Akshat412/SDP-Team-31/Data/Fall 2022/app_test.xlsx

Distance | Strength | Success | Distance | Strength | Success
1 | -70 | 1 | 3 | -83 | 1
2 | -76 | 1
3 | -87 | 1
