Akshat412/SDP-Team-31/Data/Spring 2023/Soft/collision_test_soft_2nd_4_21.csv

Magnitude
0.64
1.01
1.4
1.72
1.41
1.46
12
1.98
1.89
2.04
2.02
2.18
1.58
1.99
1.77
2.04
1.97
1.67
1.96
1.96
1.98
2.06
1.74
1.96
1.84
1.99
1.69
1.83
1.9
1.83
1.96
1.7
1.93
1.77
2.02
1.81
1.89
2.06
1.39
1.55
1.87
1.61
1.49
1.67
1.89
1.62
1.68
1.34
1.72
1.76
1.86
1.9
1.69
1.46
1.67
1.43
1.8
1.62
1.85
1.39
1.69
1.58
1.79
1.57
1.66
1.69
1.39
1.21
1.5
1.68
1.57
1.38
1.5
1.38
1.5
1.41
1.42
1.42
1.71
1.39
1.57
1.8
1.86
1.43
1.62
1.4
1.6
1.22
1
1.39
1.62
1.48
1.49
1.18
1.24
1.6
1.31
1.27
1.69
1.3
1.2
1.38
1.06
1.12
1.27
1.43
1.43
1.5
1.18
1.43
1.19
1.33
1.43
1.08
1.52
1.27
1.2
1.15
1.28
1.33
1.16
1.18
1.4
1.23
0.98
1.15
1.43
1
0.88
0.71
0.78
1.4
1.32
1.06
1.2
1.1
1.02
1.33
1.42
1.26
1.06
0.75
0.88
1.18
1.03
1.19
1.02
1.23
1.21
1.06
0.78
0.84
0.98
1.18
1.13
1
0.97
0.79
1.18
0.93
0.83
0.79
0.83
1.08
0.98
1.16
0.75
0.98
0.93
1.13
1
0.84
0.93
0.62
1.21
1.06
0.88
0.75
0.98
0.88
1.18
0.77
1.03
1.02
0.9
1
0.44
1.1
1.2
1.1
0.81
0.75
0.84
0.92
0.72
0.6
1.36
0.98
0.81
0.89
0.97
1.1
1.04
1.1
0.84
0.93
0.92
0.84
0.84
1.1
0.71
1.15
1.08
0.97
0.88
1.09
1.08
1.21
0.93
1.49
1.14
1.22
1.17
0.44
0.9
1.1
0.89
0.71
1.35
0.89
1.08
1.15
1.1
0.89
1.22
1.07
0.89
1.1
1.21
0.77
0.95
0.84
0.93
1.5
1.03
1.21
1.24
1.07
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
