Akshat412/SDP-Team-31/Data/Spring 2023/Soft/collision_test_soft_4_21.csv

Magnitude
0.03
1.06
1.42
1.48
1.4
1.38
1.04
1.41
1.52
1.34
1.38
1.38
1.43
1.1
1.29
1.31
1.47
1.37
1.81
1.4
1.57
1.76
1.29
1.48
1.48
1.67
1.62
1.5
1.49
1.67
1.18
1.69
1.65
1.67
1.21
1.48
1.57
1.5
1.48
1.47
1.57
1.47
1.68
1.47
1.29
1.77
1.18
1.86
1.77
1.4
1.57
1.37
1.47
1.57
1.57
1.57
1.58
1.57
1.47
1.38
1.7
1.67
1.47
1.47
1.51
1.28
1.57
1.19
1.57
1.58
1.19
1.31
1.28
1.67
1.6
1.47
1.49
1.67
1.52
1.68
1.58
1.52
1.27
1.69
1.47
1.59
1.18
1.55
1.5
1.69
1.42
1.27
1.29
1.47
1.31
1.26
1.76
1.67
1.51
1.47
1.27
1.6
1.08
1.67
1.37
1.48
1.47
1.39
1.39
1.47
1.6
1.27
1.47
1.48
1.48
1.47
1.47
1.6
1.58
1.38
1.29
1.31
1.33
1.02
1.67
1.52
1.48
1.67
1
1.47
1.47
1.69
1.47
1.18
1.58
1.38
1.67
1.41
1.77
1.48
1.4
1.81
1.37
1.31
1.68
1.37
1.57
1.38
1.39
1.83
1.28
1.28
1.36
1.28
1.29
1.57
1.41
1.21
1.47
1.42
1.37
1.5
1.39
1.29
1.4
1.47
1.28
1.15
1.57
1.37
1.69
1.38
1.38
1.39
1.2
1.39
1.08
1.27
1.38
1.41
1.37
1.2
1.27
1.27
1.27
1.48
1.1
1.33
1.3
1.19
0.98
1.38
1.28
1.57
1.39
1.48
1.38
1.27
1.77
1.18
1.38
1.52
1.37
1.27
1.31
1.47
1.27
1.4
1.76
1.24
1.33
1.38
1.61
1.18
1.18
1.47
1.29
1.49
1.23
1.31
1.4
1.21
1.38
1.31
1.4
1.5
1.08
1.47
1.57
1.38
1.52
1.47
1.62
1.19
1.76
1.38
1.43
1.29
1.46
1.39
1.18
1.33
1.43
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
