Akshat412/SDP-Team-31/Data/Spring 2023/collision_test_4_21.csv

Magnitude | Sampled at 3200 Hz
1.35
1.35
1.62
1.57
1.29
1.55
1.58
1.46
1.31
1.54
1.08
1.44
1.52
1.52
1.11
1.41
1.76
1.26
1.29
1.65
1.16
1.61
1.41
1.46
1.34
1.28
1.2
1.55
1.16
1.41
1.14
1.21
1.12
1.16
1.42
1.27
1.51
1.51
1.25
0.98
1.42
1.37
1.28
1.42
0.39
1.13
1.09
1.08
1.19
1.25
1.18
1.32
1.43
1.58
1.4
1.12
1.16
1.27
1
1.29
1.46
1.26
1.07
1.35
1.1
1.37
1
1.37
1.47
1.31
1.21
1.33
0.93
1.15
1.15
1.29
1.59
1.18
1.36
1.34
0.98
1.1
1.52
1.26
1.18
1.2
1.48
1.64
1.78
1.15
1.26
1.69
0.89
1.18
1.46
1.48
1.74
1.27
1.46
1.37
1.27
1.14
1.43
1
1.56
1.34
1.29
1.67
1.29
1.46
1.15
1.24
1.22
1.28
1.51
1.42
1.2
1.25
1.39
1.12
1.27
1.31
1.51
1.22
1.32
1.48
1.5
1.38
1.29
1.22
1.22
1.21
1.25
1.21
1.52
1.38
1.18
1.44
1.43
1.55
1.42
1.39
1.56
1.38
1.4
1.42
1.35
1.29
1.47
1.31
1.62
1.13
1.31
1.51
1.4
1.19
1.32
1.51
1.06
1.46
1.41
1.4
1.42
1.26
1.27
1.34
1.27
1.29
1.61
1.27
1.51
1.42
1.1
1.18
1.18
1.62
1.46
1.2
1.26
1.62
1.53
1.29
1.69
1.43
1.32
1.46
1.16
0.92
1.36
1.18
1.18
1.25
1.43
1.31
1.18
1.22
1.34
1.33
1.2
1.23
1.53
1.24
1.48
1.41
1.72
1.15
0.98
1.43
1.32
1.18
1.46
1.66
1.63
1.51
1.52
1.86
1.99
0.93
1.29
1.29
1.48
1.61
1.24
1.18
1.31
1.39
1.58
1.27
1.61
1.63
1.51
1.26
1.27
1.39
1.64
1.23
1.18
1.63
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
