Akshat412/SDP-Team-31/Firmware/Testing/bleTest/bleTest.ino

#include <Arduino.h>
#include <SPI.h>
#include "Adafruit_BLE.h"
#include "Adafruit_BluefruitLE_SPI.h"
#include "Adafruit_BluefruitLE_UART.h"

#include "BluefruitConfig.h"

/*=========================================================================
    APPLICATION SETTINGS

? ? FACTORYRESET_ENABLE? ?  Perform a factory reset when running this sketch
? ?
? ?                         Enabling this will put your Bluefruit LE module
                            in a 'known good' state and clear any config
                            data set in previous sketches or projects, so
? ?                         running this at least once is a good idea.
? ?
? ?                         When deploying your project, however, you will
                            want to disable factory reset by setting this
                            value to 0.? If you are making changes to your
? ?                         Bluefruit LE device via AT commands, and those
                            changes aren't persisting across resets, this
                            is the reason why.? Factory reset will erase
                            the non-volatile memory where config data is
                            stored, setting it back to factory default
                            values.
? ? ? ?
? ?                         Some sketches that require you to bond to a
                            central device (HID mouse, keyboard, etc.)
                            won't work at all with this feature enabled
                            since the factory reset will clear all of the
                            bonding data stored on the chip, meaning the
                            central device won't be able to reconnect.
    -----------------------------------------------------------------------*/
    #define FACTORYRESET_ENABLE      1
/*=========================================================================*/


/* ...hardware SPI, using SCK/MOSI/MISO hardware SPI pins and then user selected CS/IRQ/RST */
Adafruit_BluefruitLE_SPI ble(BLUEFRUIT_SPI_CS, BLUEFRUIT_SPI_IRQ, BLUEFRUIT_SPI_RST);


// A small helper
void error(const __FlashStringHelper*err) {
  Serial.println(err);
  while (1);
}

/**************************************************************************/
/*!
    @brief  Sets up the HW an the BLE module (this function is called
            automatically on startup)
*/
/**************************************************************************/
void setup(void)
{  
  Serial.begin(115200);
  while (!Serial); // Waiting for Serial Monitor
  Serial.println(F("Adafruit Bluefruit AT Command Example"));
  Serial.println(F("-------------------------------------"));

  /* Initialise the module */
  Serial.println(F("Initialising the Bluefruit LE module: "));

  if ( !ble.begin(VERBOSE_MODE) )
  {
    error(F("Couldn't find Bluefruit, make sure it's in CoMmanD mode & check wiring?"));
  }
  
  if ( FACTORYRESET_ENABLE )
  {
    Serial.println(F("Performing a factory reset: "));
    if ( ! ble.factoryReset() ){
      error(F("Couldn't factory reset"));
    }
  }

  // disable echo from console 
  ble.echo(false);

  // define new service with UUID 0x180E
  ble.println("AT+GATTADDSERVICE=UUID=0x180E");
  ble.waitForOK();  

  // define new characteristic with UUID 0x2A46
  ble.println("AT+GATTADDCHAR=UUID=0x2A46,PROPERTIES=0x02,MIN_LEN=1,VALUE=65");
  ble.waitForOK(); 

  ble.println("ATZ");
  ble.waitForOK(); 

  pinMode(LED_BUILTIN, OUTPUT); 
}

/**************************************************************************/
/*!
    @brief  Constantly poll for new command or response data
*/
/**************************************************************************/
void loop(void) 
{
  ble.println("AT+GATTCHAR=1,75");
  ble.waitForOK(); 
  digitalWrite(LED_BUILTIN, HIGH); 

  delay(3000);

  ble.println("AT+GATTCHAR=1,65");
  ble.waitForOK(); 
  digitalWrite(LED_BUILTIN, LOW); 
  
  delay(3000);
}
