Akshat412/SDP-Team-31/Firmware/Testing/ForceSensor/ForceSensor.ino

/* FSR testing sketch. 
 
Connect one end of FSR to 5V, the other end to Analog 0.
Then connect one end of a 10K resistor from Analog 0 to ground
Connect LED from pin 11 through a resistor to ground 
 
For more information see www.ladyada.net/learn/sensors/fsr.html */
 
int fsrAnalogPin = A3;   // FSR is connected to analog 0
int LEDpin = 9;         // connect Red LED to pin 11 (PWM pin)
int fsrReading;         // the analog reading from the FSR resistor divider
int LEDbrightness;
 
void setup(void) {
  Serial.begin(115200);
  pinMode(LEDpin, OUTPUT);
  digitalWrite(LEDpin, HIGH); 
}
 
void loop(void) {
  fsrReading = analogRead(fsrAnalogPin);
  Serial.print("Analog reading = ");
  Serial.println(fsrReading);
 
  if(fsrReading > 75) digitalWrite(LEDpin, HIGH); 
  else digitalWrite(LEDpin, LOW); 
}
